RobMink/Polar/PSUMount.stl

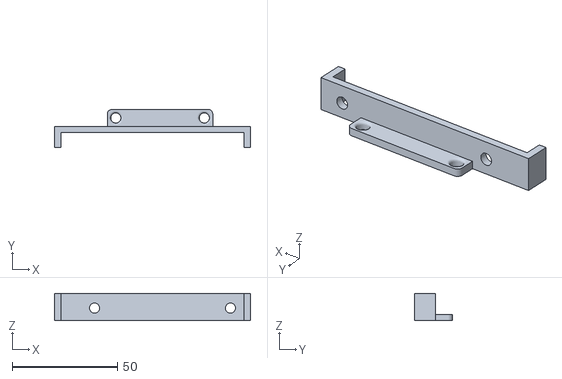
[picture p16: CAD file, 2019-10-16]
PSUMount.stl
93.0 x 18.0 x 13.0
