RobMink/Polar/pipemount-wire.stl

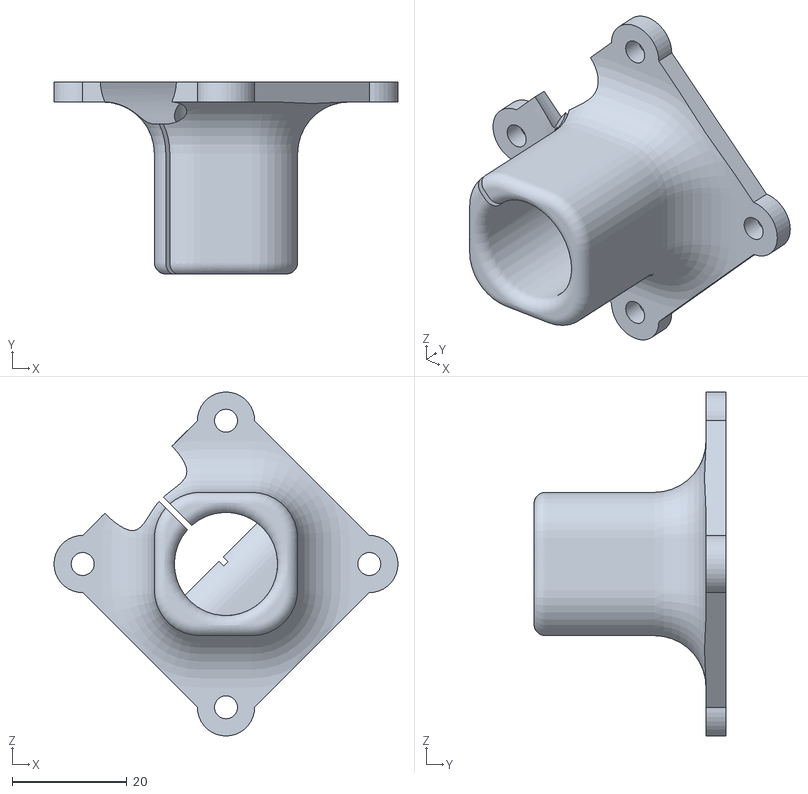
[picture p17: CAD file, 2019-10-16]
pipemount-wire.stl
60.0 x 33.5 x 60.0
