RobMink/Polar/zthreadedrod.stl

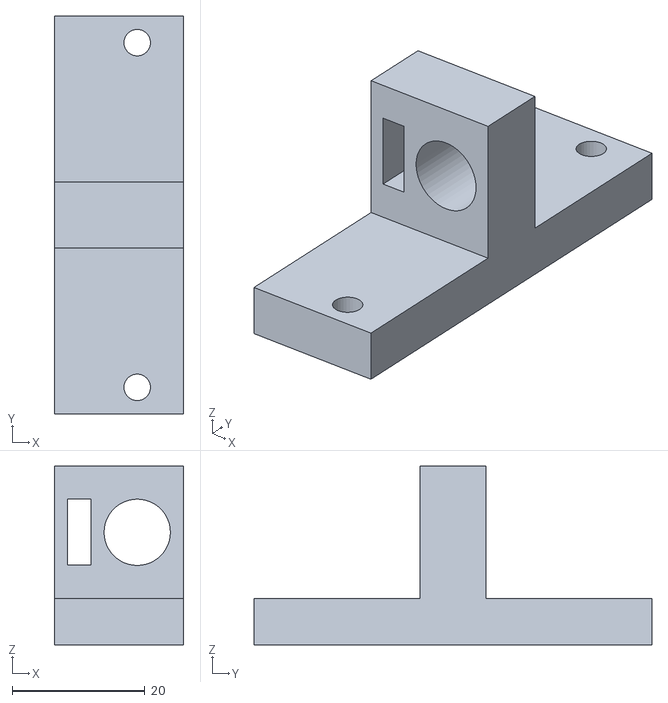
[picture p18: CAD file, 2019-10-16]
zthreadedrod.stl
19.5 x 60.0 x 27.0
