RobMink/Polar/bedtiedown2.stl

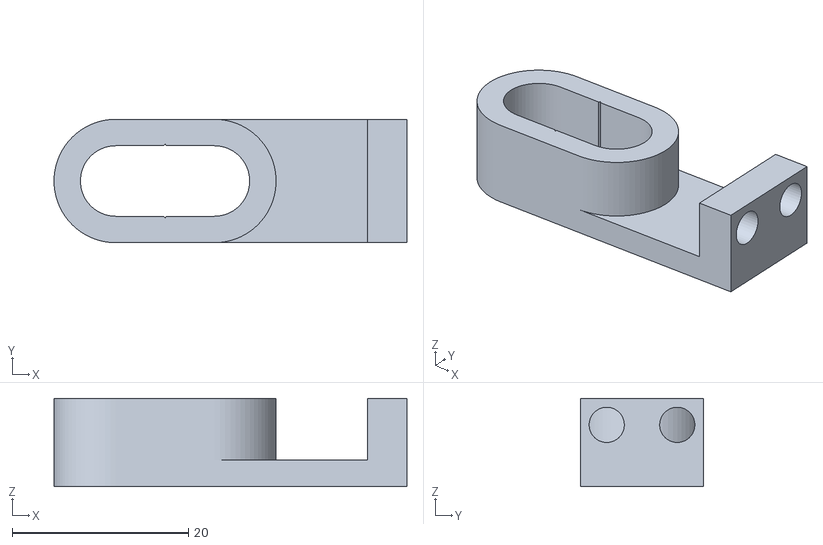
[picture p19: CAD file, 2019-10-16]
bedtiedown2.stl
40.0 x 14.0 x 10.0
