RobMink/Polar/radianprinterbase2-chopped.stl

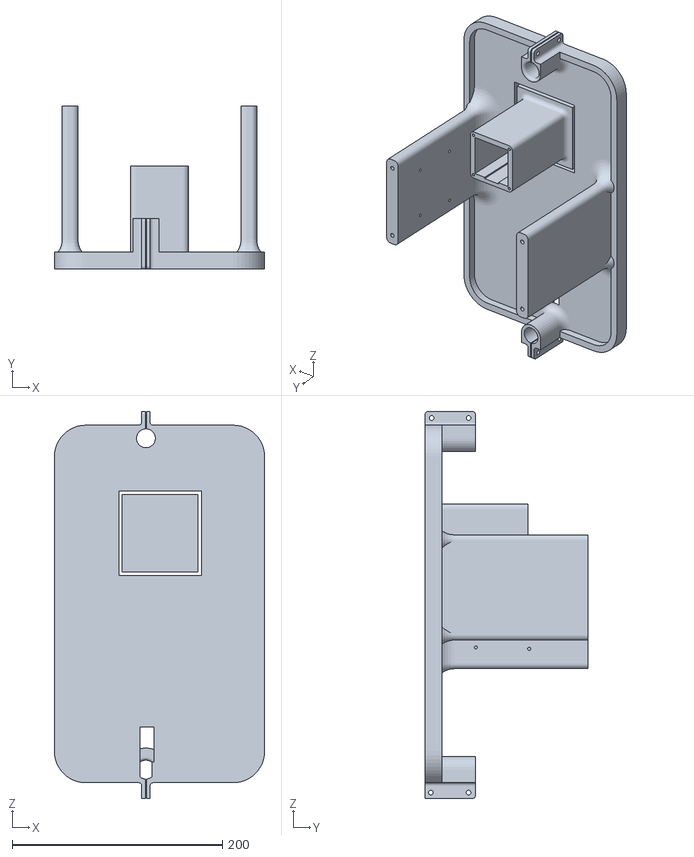
[picture p20: CAD file, 2019-10-16]
radianprinterbase2-chopped.stl
200.0 x 155.0 x 368.0
