RobMink/Polar/gantry-Z-slider.stl

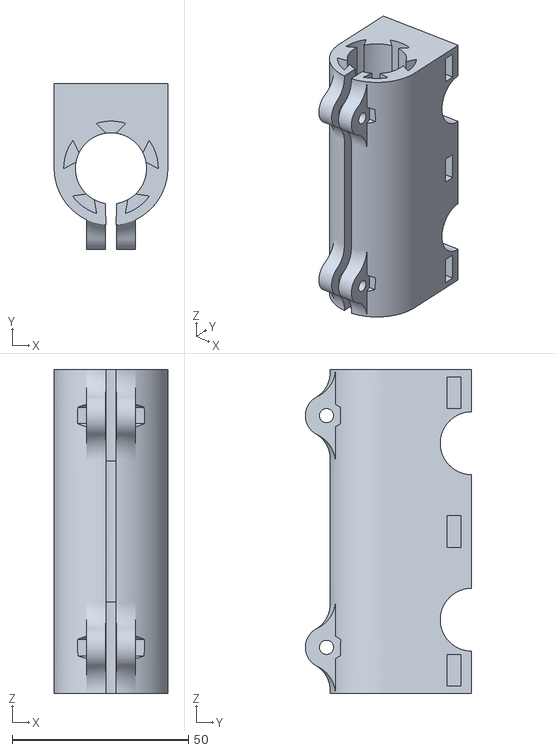
[picture p21: CAD file, 2019-10-16]
gantry-Z-slider.stl
32.2 x 47.1 x 91.8
