RobMink/Polar/radianprintercoupler.stl

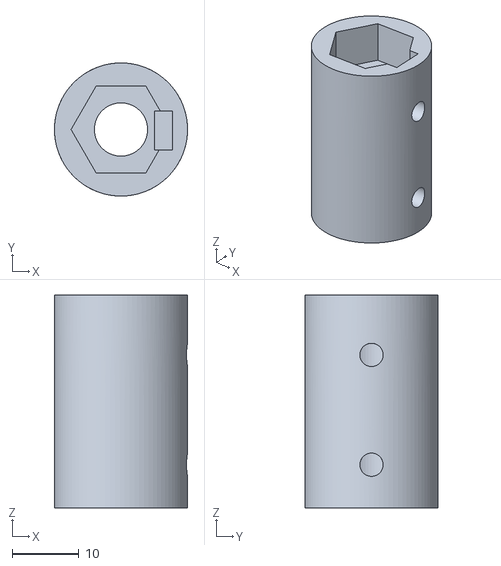
[picture p22: CAD file, 2019-10-16]
radianprintercoupler.stl
20.0 x 20.0 x 32.0
