RobMink/Polar/radiouscarrage.stl

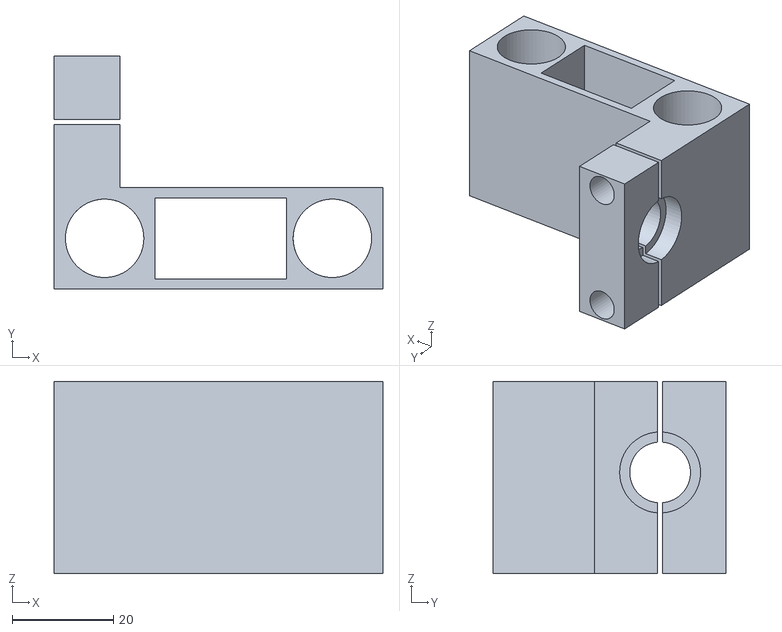
[picture p23: CAD file, 2019-10-16]
radiouscarrage.stl
65.0 x 46.0 x 38.0
